probe-rs/hive/renders_3dmodels/Assembly/rpi4b.step

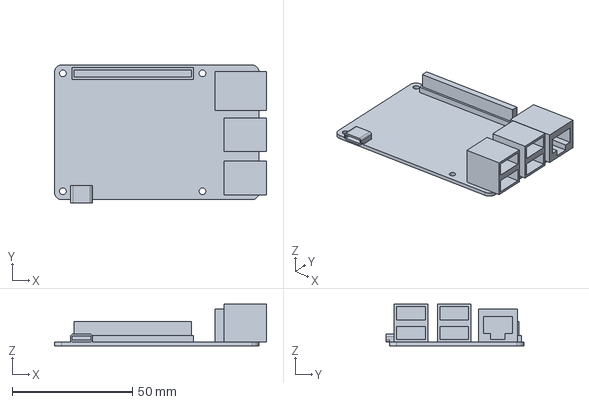
[picture p20: CAD file, 2021-10-07]
renders_3dmodels/Assembly/rpi4b.step
88.1 x 57.4 x 17.3 mm
