probe-rs/hive/component_library/3d_models/FTSH-105-01-F-DV-007-K.stp

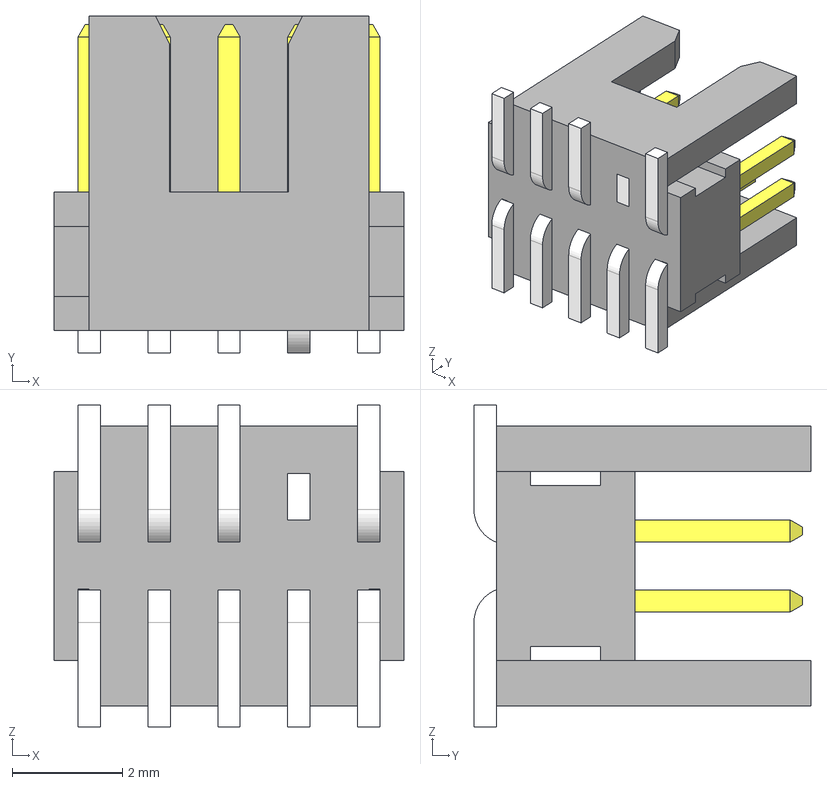
[picture p21: CAD file, 2021-09-30]
component_library/3d_models/FTSH-105-01-F-DV-007-K.stp
6.35 x 6.12 x 5.84 mm
_FTSH-105-01-F-DV-007-K_body
_FTSH-105-01-F-DV-007-K_pins1
_FTSH-105-01-F-DV-007-K_pins2
