probe-rs/hive/component_library/3d_models/ESQ-113-24-L-D.stp

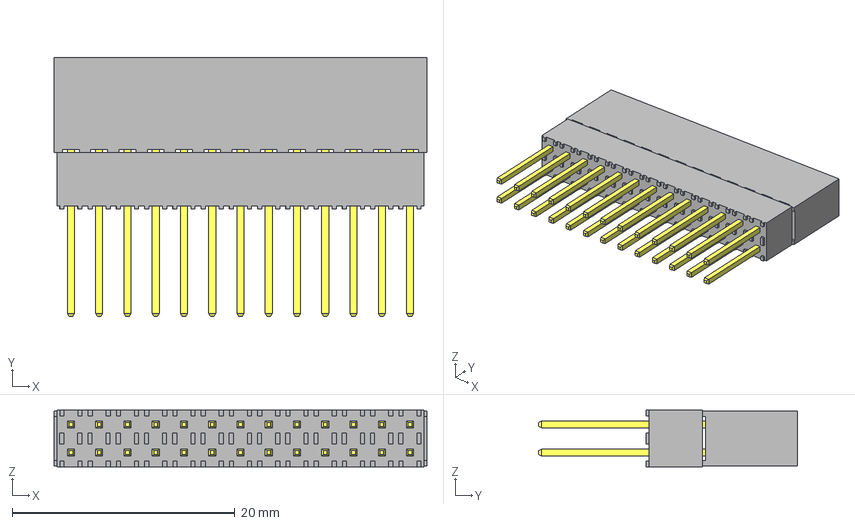
[picture p22: CAD file, 2021-09-30]
component_library/3d_models/ESQ-113-24-L-D.stp
33.5 x 23.2 x 5.08 mm
_ESQ-113-24-L-D_socket
_ESQ-113-24-L-D_pins
_ESQ-113-24-G-D-LL_bpins
