probe-rs/hive/component_library/3d_models/KRTB_AILMS1-5B5C-B1B12-0-R18.stp

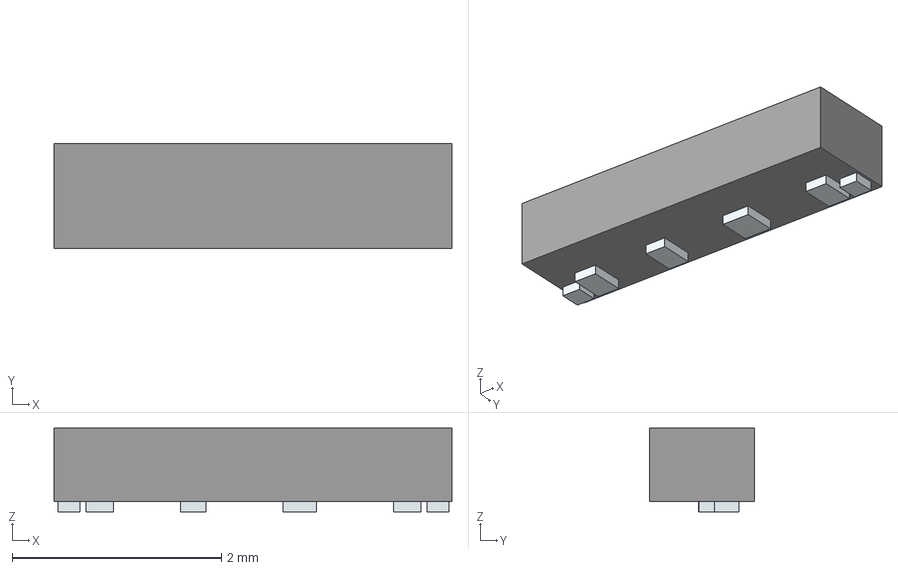
[picture p23: CAD file, 2021-09-26]
component_library/3d_models/KRTB_AILMS1-5B5C-B1B12-0-R18.stp
3.80 x 1.00 x 0.8 mm
Pins
