probe-rs/hive/component_library/3d_models/CUI_DEVICES_RDS-10S-74385-SMT.step

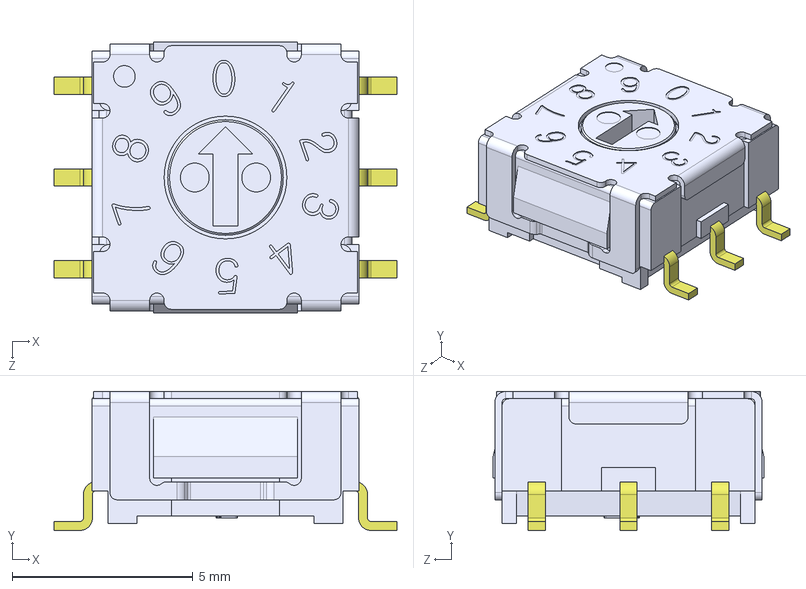
[picture p24: CAD file, 2021-09-23]
component_library/3d_models/CUI_DEVICES_RDS-10S-74385-SMT.step
9.50 x 3.85 x 7.50 mm
RDS74365 housing
RDS74385_SMT_pins
RDS74365_10_face plate
RDS74365_actuator_10S
