probe-rs/hive/component_library/3d_models/NCP1117DT33T5G.STEP

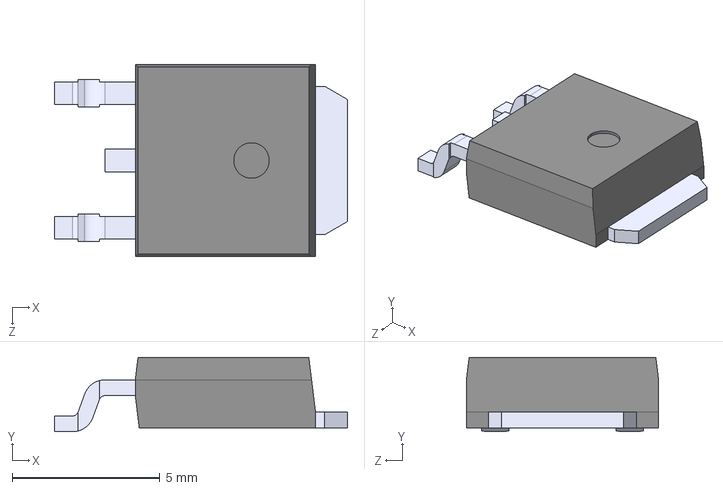
[picture p25: CAD file, 2021-09-22]
component_library/3d_models/NCP1117DT33T5G.STEP
9.91 x 2.51 x 6.50 mm
